RehanShakir/SmartAgri/Circuit/npk.jpg

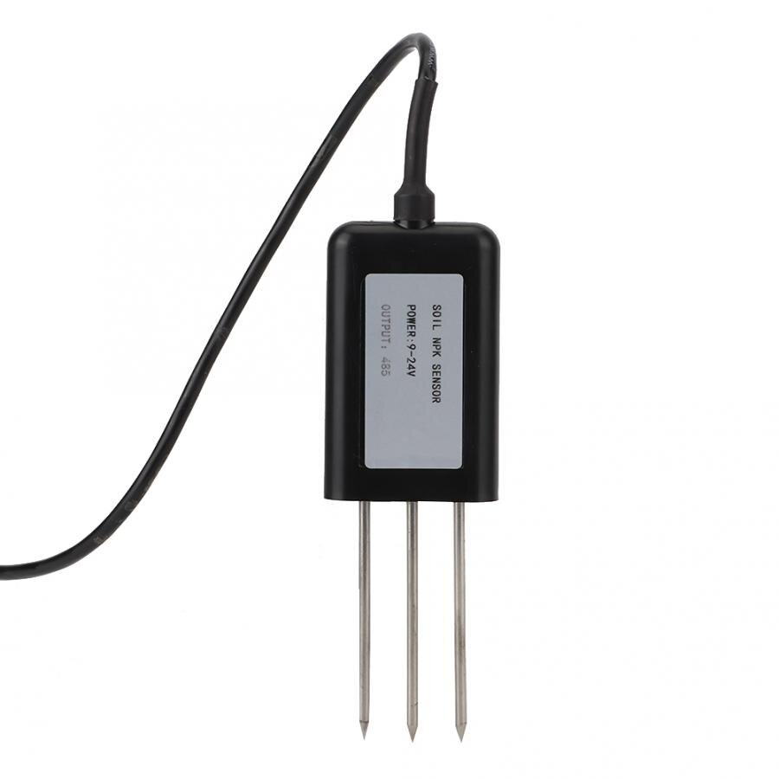
Circuit/npk.jpg
