RehanShakir/SmartAgri/Circuit/ttlrs485.jpg

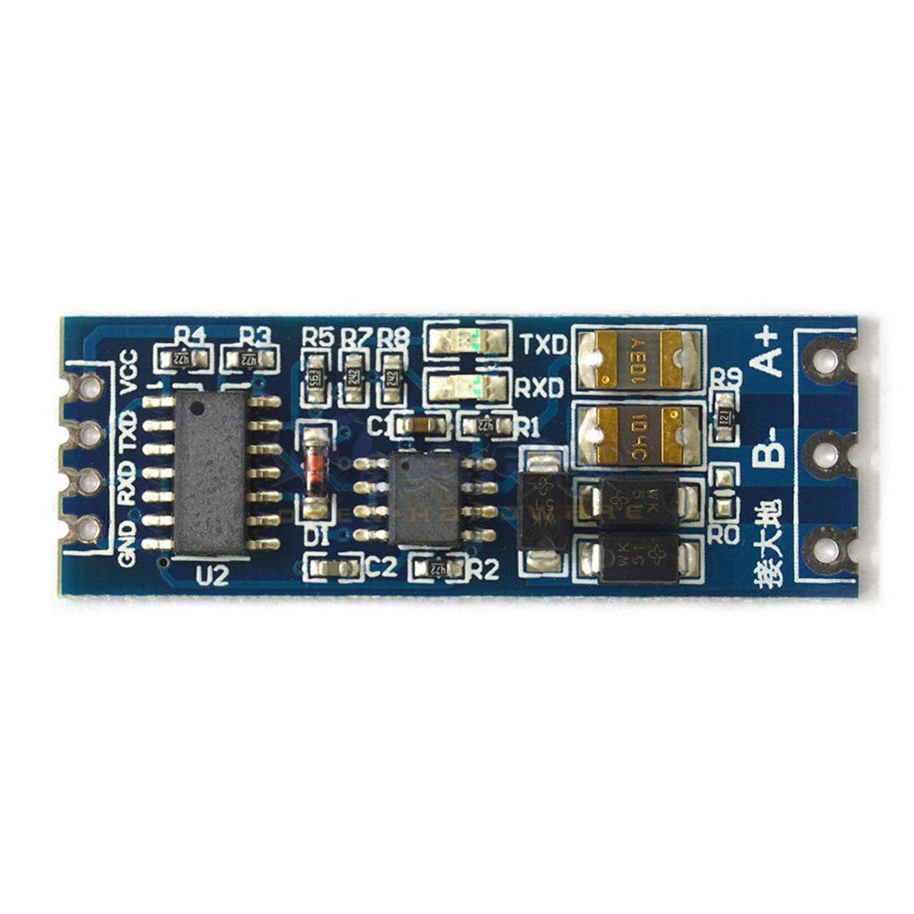
Circuit/ttlrs485.jpg
