RehanShakir/SmartAgri/SmartphoneApp/ic_launcher/1024.png

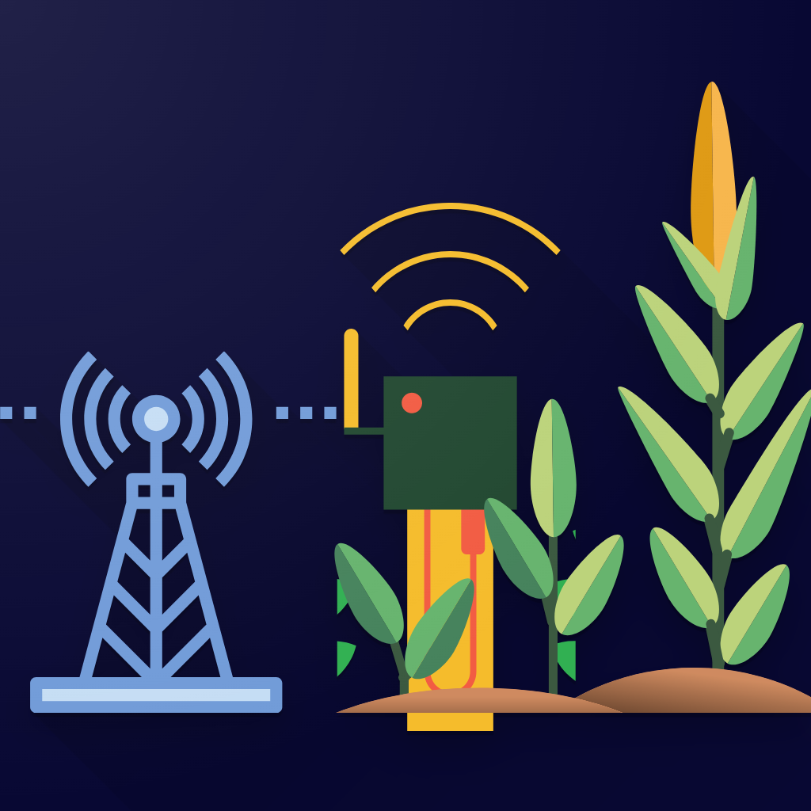
SmartphoneApp/ic_launcher/1024.png
