RehanShakir/SmartAgri/SmartphoneApp/SmartAgri (1024 x 1024 px).png

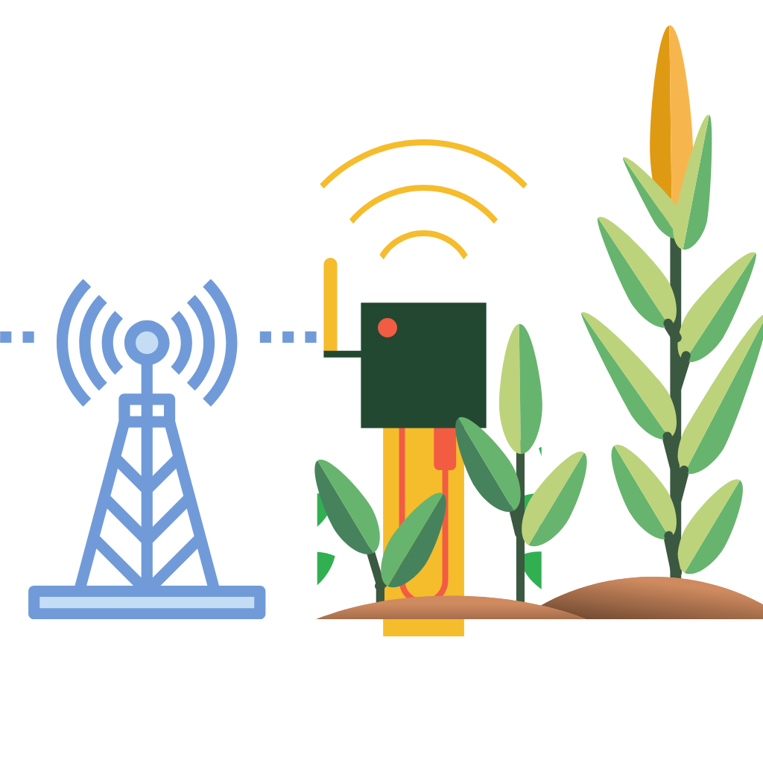
SmartphoneApp/SmartAgri (1024 x 1024 px).png
